RetroIsTheNewBlack/retrobox/MM_Empty_Tray.stl

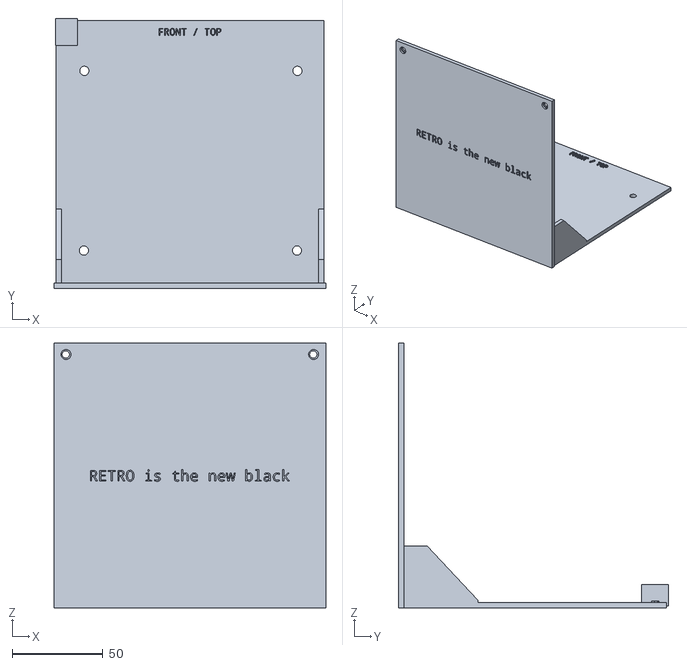
[picture p19: CAD file, 2026-09-11]
MM_Empty_Tray.stl
150.0 x 149.0 x 146.0
