RetroIsTheNewBlack/retrobox/MM_Buttoncover_only_no_USB.stl

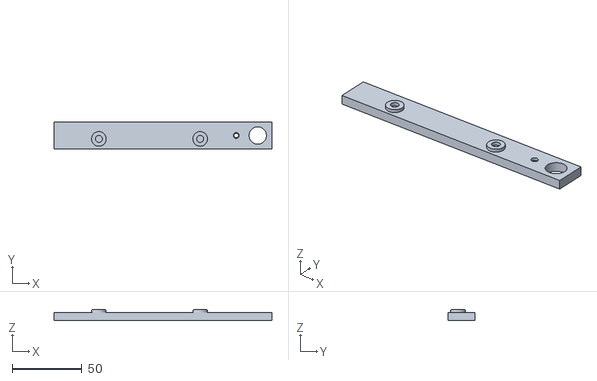
[picture p20: CAD file, 2026-09-11]
MM_Buttoncover_only_no_USB.stl
156.0 x 19.5 x 7.60
