RetroIsTheNewBlack/retrobox/MM_Blind_Square.stl

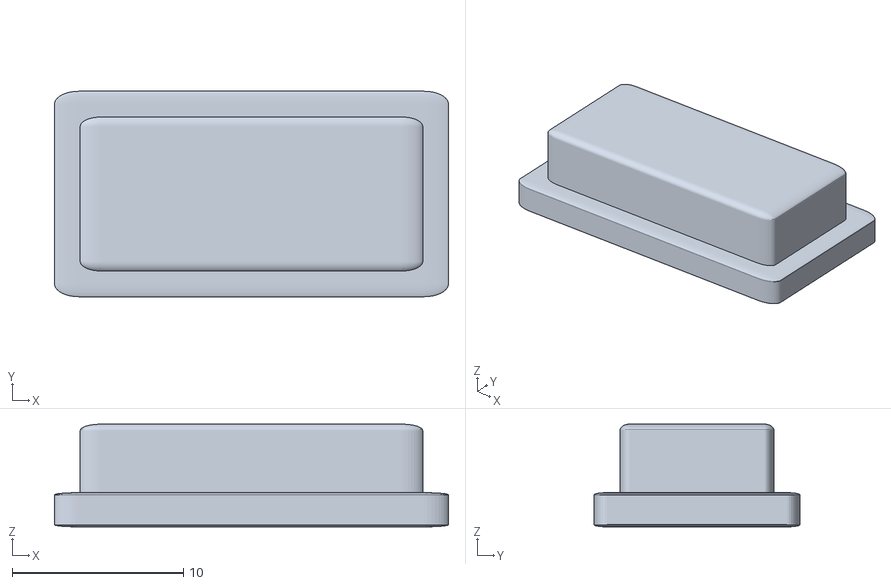
[picture p21: CAD file, 2026-09-11]
MM_Blind_Square.stl
23.0 x 12.0 x 6.00
