RetroIsTheNewBlack/retrobox/MM_Button_Adapter_12mmTo6mm.stl

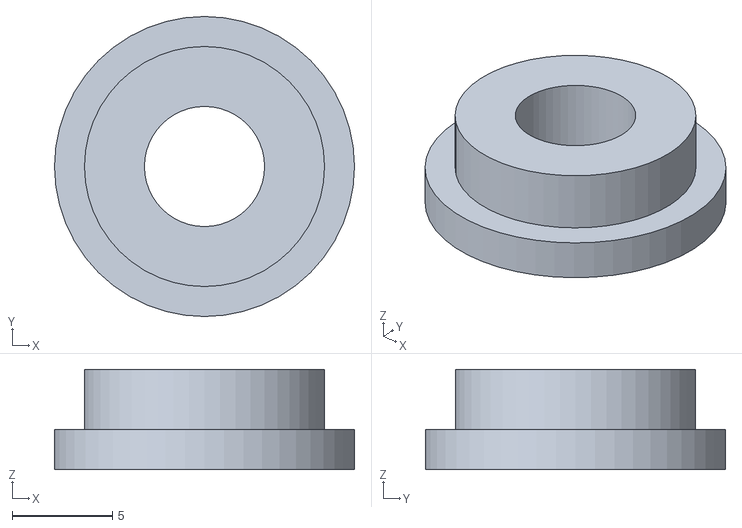
[picture p22: CAD file, 2026-09-11]
MM_Button_Adapter_12mmTo6mm.stl
15.0 x 15.0 x 5.00
