RetroIsTheNewBlack/retrobox/MM_Button.stl

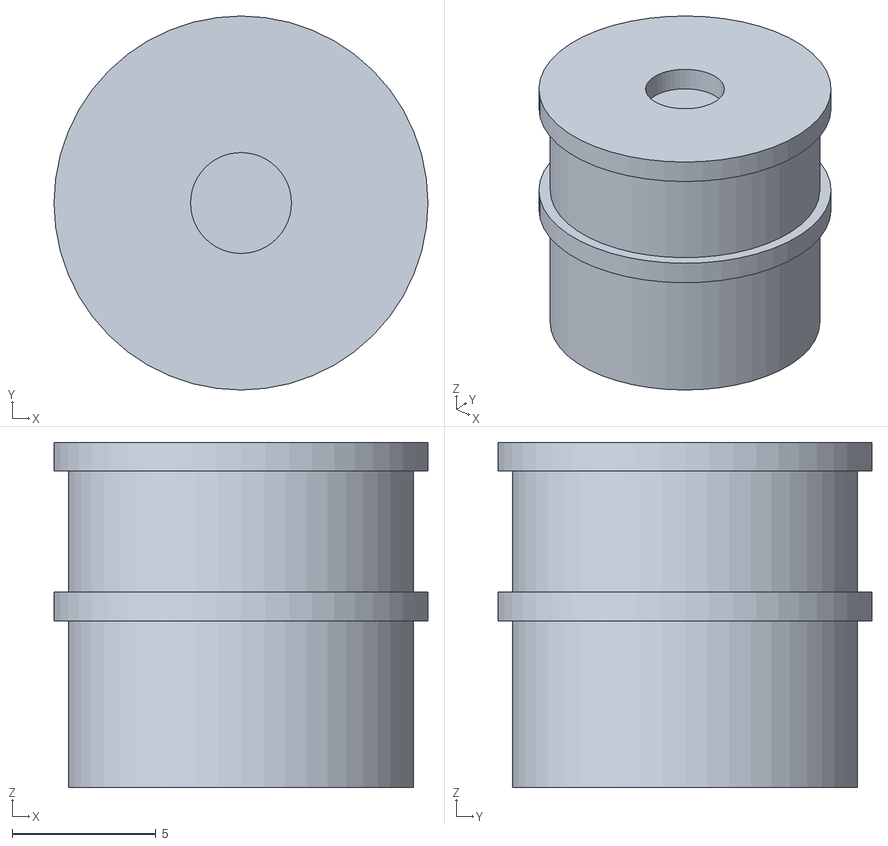
[picture p23: CAD file, 2026-09-11]
MM_Button.stl
13.0 x 13.0 x 12.0
