RetroIsTheNewBlack/retrobox/MM_Blind_Round.stl

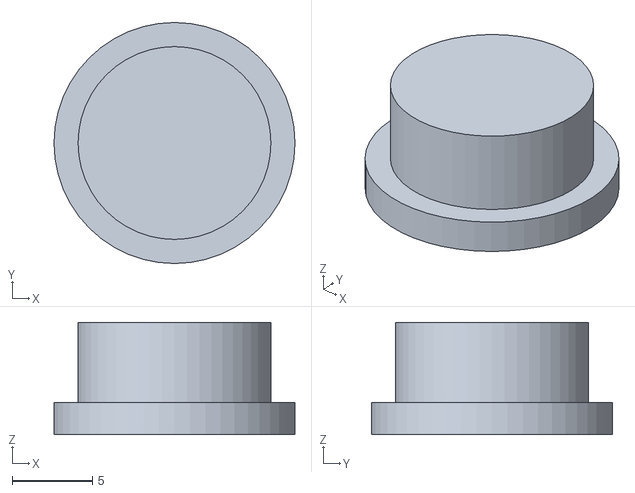
[picture p24: CAD file, 2026-09-11]
MM_Blind_Round.stl
15.0 x 15.0 x 7.00
