RetroIsTheNewBlack/retrobox/images/1.JPG

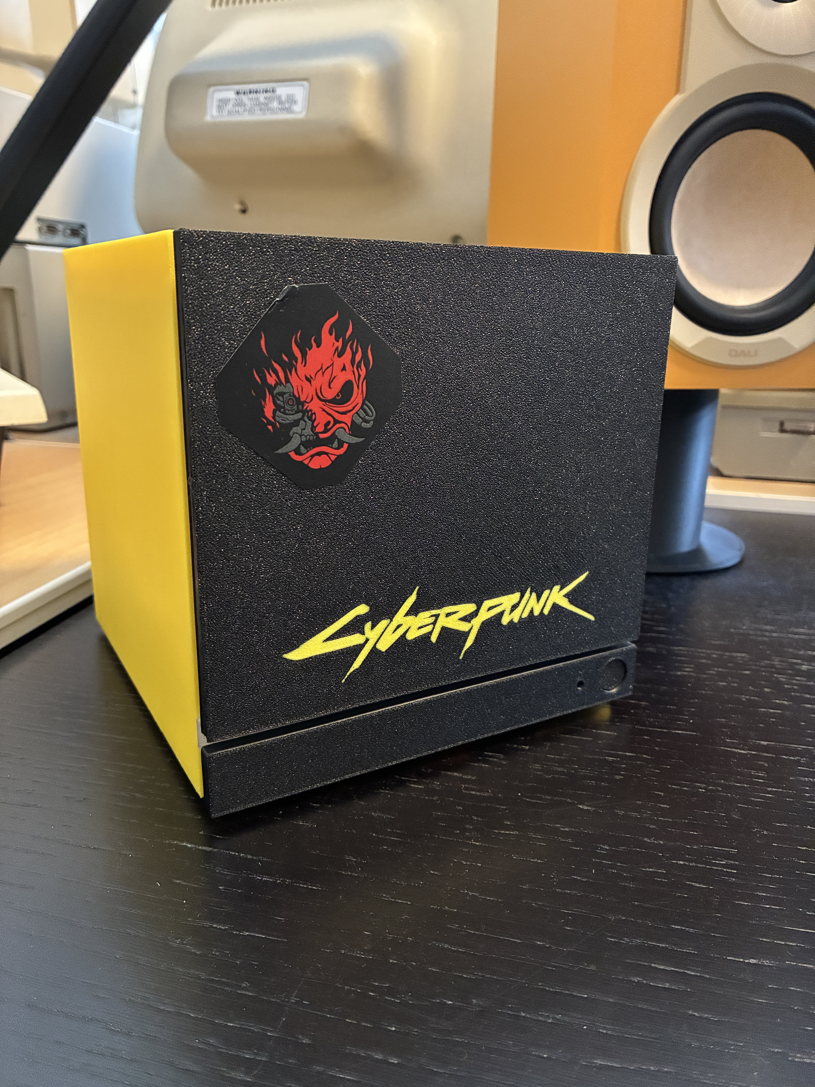
images/1.JPG
